dreamshader/smartTFT/doc/img/ceramic-capacitor-001uF.jpg

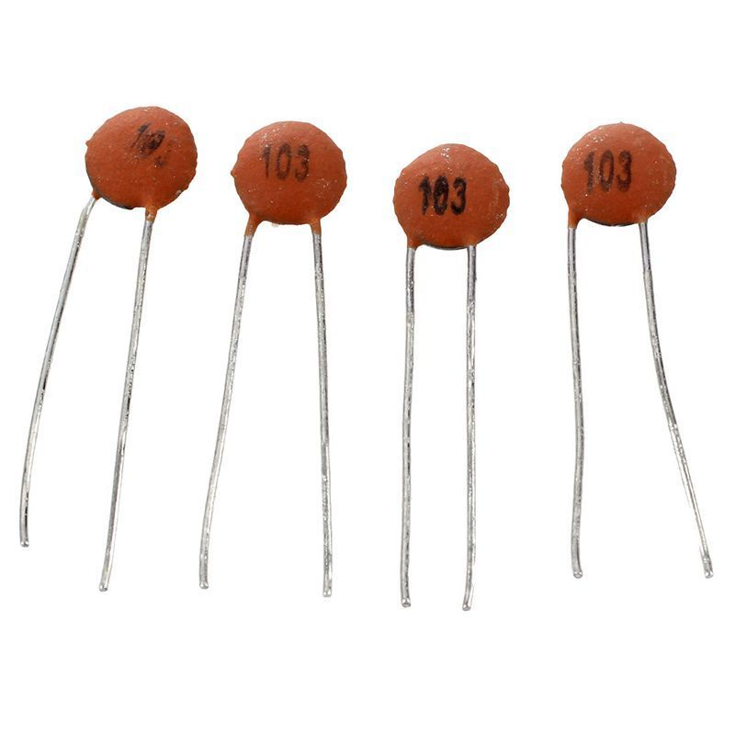
doc/img/ceramic-capacitor-001uF.jpg
