dreamshader/smartTFT/doc/img/pinheader-male.jpg

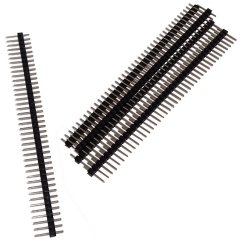
doc/img/pinheader-male.jpg
