dreamshader/smartTFT/doc/img/pro-mini.jpg

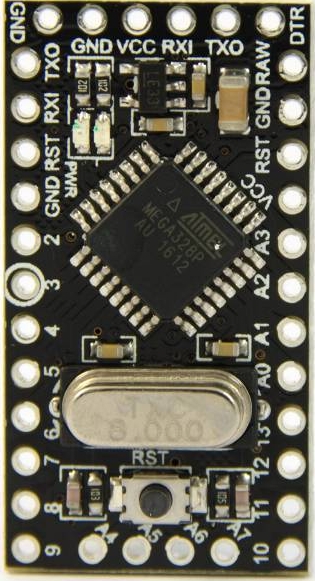
doc/img/pro-mini.jpg
