dreamshader/smartTFT/doc/img/protoboard-punkt-streifen.jpg

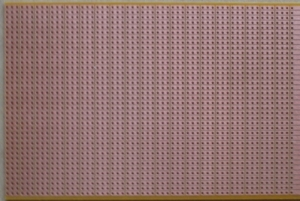
doc/img/protoboard-punkt-streifen.jpg
