dreamshader/smartTFT/doc/img/smartTFT-cura-bottom-small.png

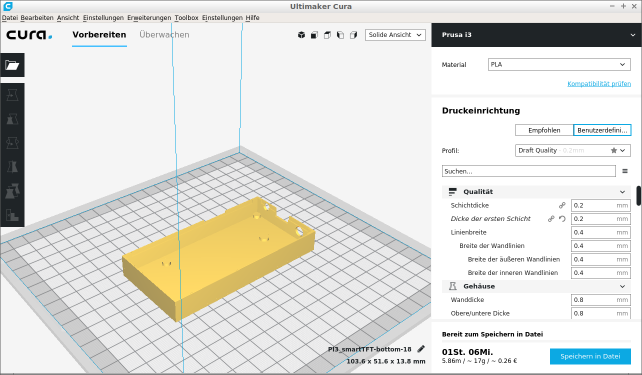
doc/img/smartTFT-cura-bottom-small.png
