dreamshader/smartTFT/doc/img/smartTFT-proto2-small.jpg

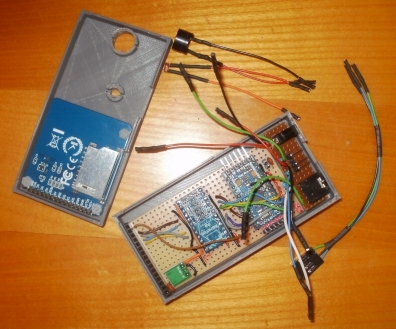
doc/img/smartTFT-proto2-small.jpg
