dreamshader/smartTFT/doc/img/smartTFT-proto3-small.jpg

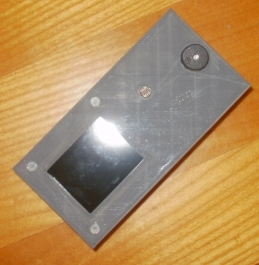
doc/img/smartTFT-proto3-small.jpg
