dreamshader/smartTFT/doc/img/wires-02.jpg

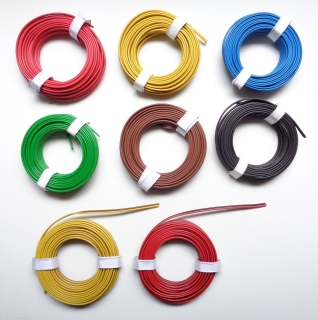
doc/img/wires-02.jpg
