dreamshader/smartTFT/fritzing/smartTFT_Steckplatine.png

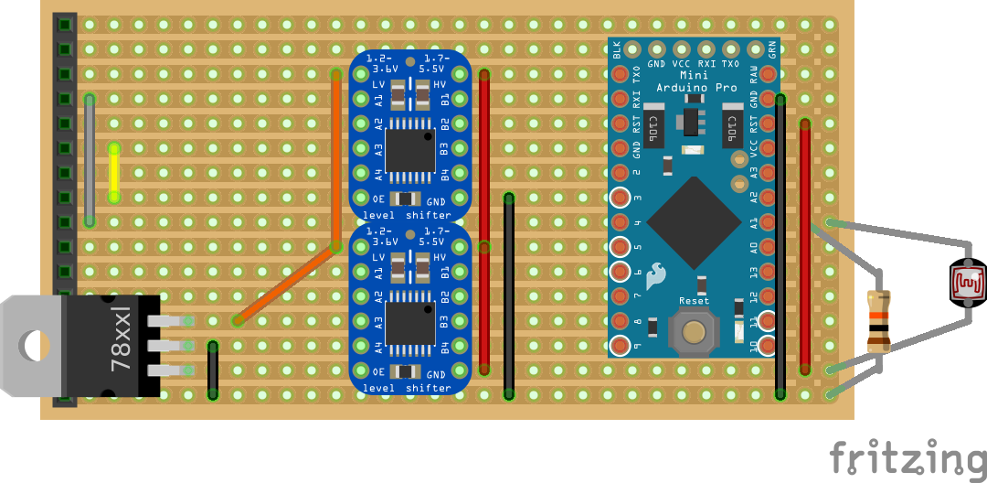
fritzing/smartTFT_Steckplatine.png
