dreamshader/smartTFT/eagle/tft-18-sd.sch

## EAGLE design eagle/tft-18-sd.sch (2018-07-11)

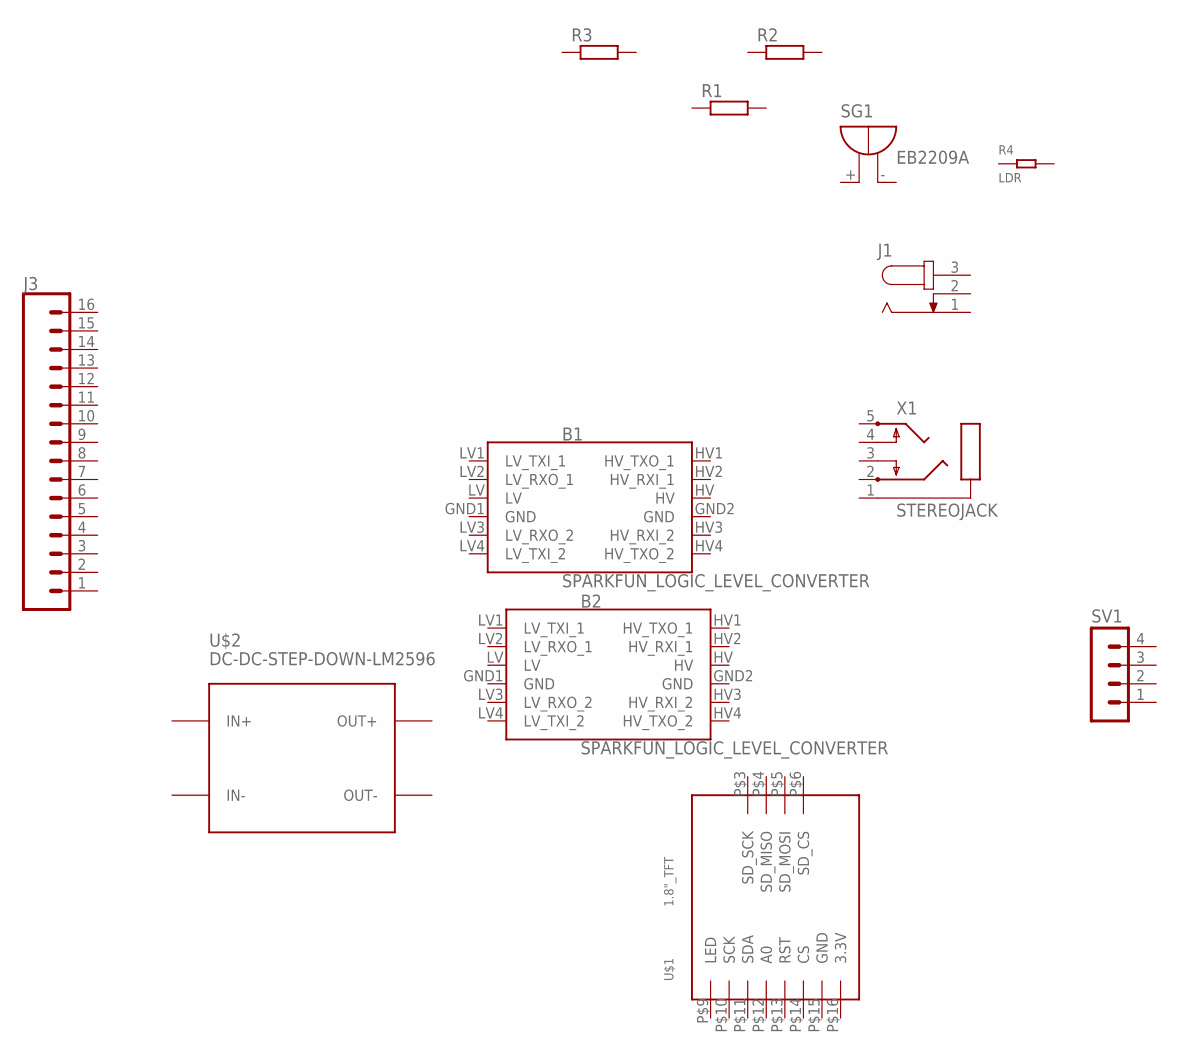
[picture p32: schematic tft-18-sd.sch]

Parts:
B1, B2: SPARKFUN_LOGIC_LEVEL_CONVERTER
J1: JACK-PLUG0; SPC4077
J3: CONN_16; 1X16
R1, R2, R3: R-EU_0207/5V; 0207/5V
R4: LDR; PR-2.8-4.2X4.9MM
SG1: EB2209A
SV1: MA04-1
U$1: 1.8"_TFT
U$2: DC-DC-STEP-DOWN-LM2596
X1: STEREOJACK; STX3100
